DavidBG88/SmartLampSE/software/smart_lamp_se/iAQCore.h

#ifndef IAQ_CORE_H
#define IAQ_CORE_H

#include <stdint.h>

#ifdef __cplusplus
extern "C" {
#endif

typedef struct IAQCORE_Reading {
    uint8_t status;
    uint16_t eco2_ppm;
    uint16_t etvoc_ppb;
    uint32_t resistance;
} IAQCORE_Reading;

void IAQCORE_init(void);

IAQCORE_Reading IAQCORE_read(void);

#ifdef __cplusplus
}
#endif

#endif  // IAQ_CORE_H
