DavidBG88/SmartLampSE/software/smart_lamp_se/spi.h

/* 
 * File:   spi-master-v1.h
 * Author: norberto
 *
 * Created on 12 de julio de 2022, 11:15
 */

#ifndef SPI_H
#define SPI_H

#include <stdint.h>

#define spi_clk PORTBbits.RB4
#define spi_dat_out PORTBbits.RB5
#define spi_dat_in PORTBbits.RB6

void SPI_init();        

uint8_t SPI_write_read(uint8_t byte);

#endif  // SPI_H
